digiampietro/enclosure-ttgo-lora32/img/enclosure3.jpg

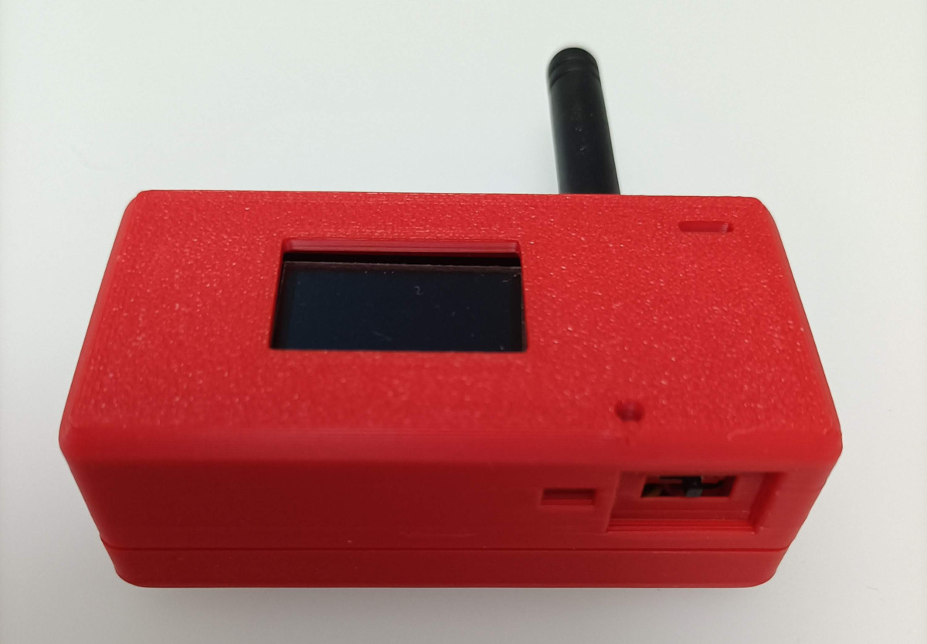
img/enclosure3.jpg
