digiampietro/enclosure-ttgo-lora32/img/enclosure5.jpg

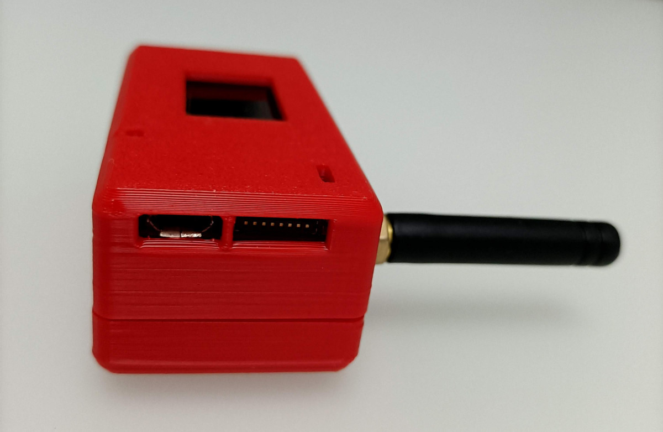
img/enclosure5.jpg
