digiampietro/enclosure-ttgo-lora32/img/enclosure7.jpg

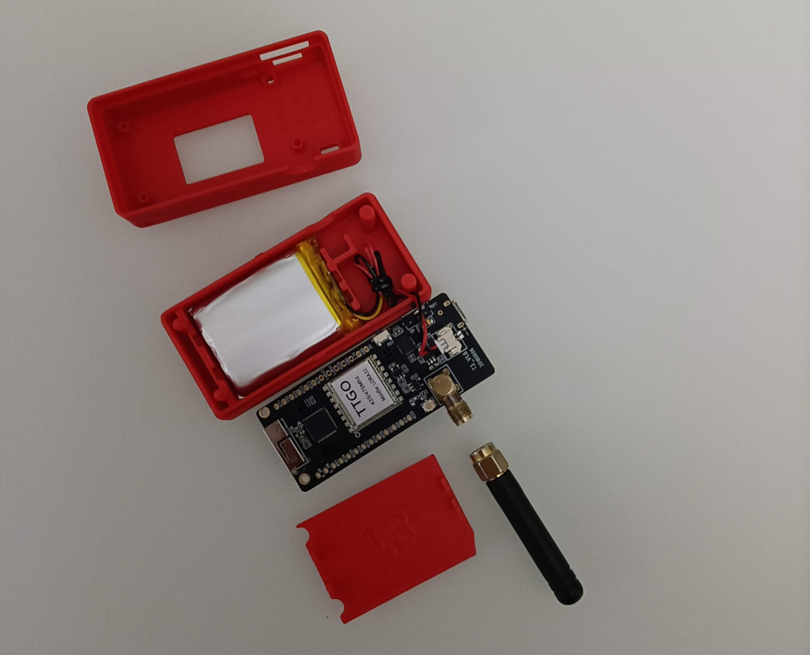
img/enclosure7.jpg
