digiampietro/enclosure-ttgo-lora32/img/enclosure10.jpg

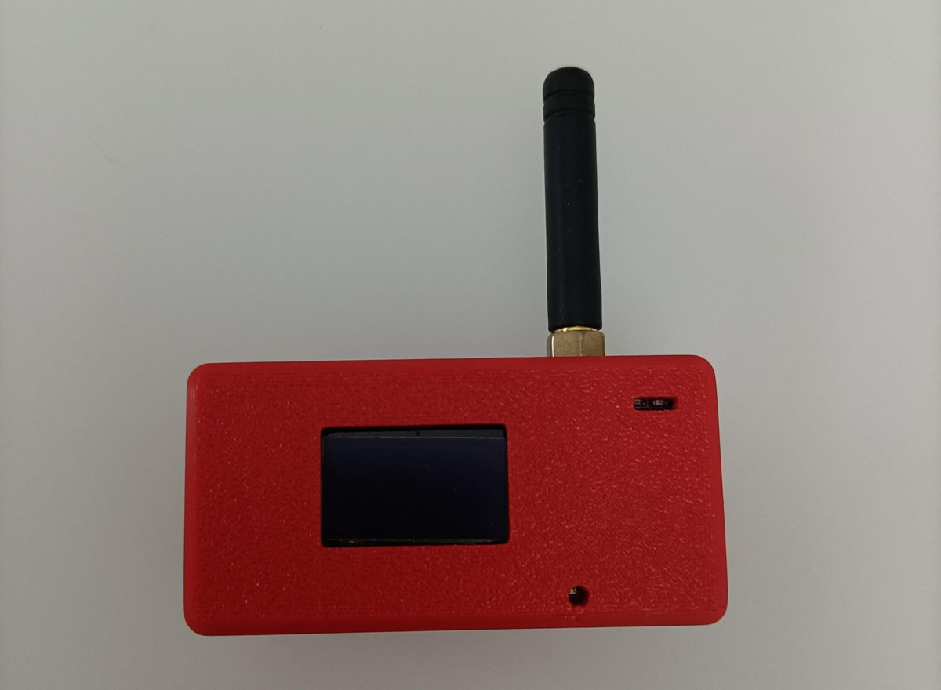
img/enclosure10.jpg
